Sir68k/md-classic-display/source/md_display/icons.h

#ifndef ICONS_7X7_H
#define ICONS_7X7_H

const static uint8_t icons_7x7[][7] = {
    {0x7f, 0x45, 0x49, 0x51, 0x49, 0x45, 0x7f}, //0 email
    {0x3e, 0x6f, 0x51, 0x01, 0x71, 0x7f, 0x3e}, //1 github
    {0x40, 0x60, 0x77, 0x77, 0x77, 0x60, 0x40}, //2 user
    {0x70, 0x7e, 0x71, 0x51, 0x71, 0x7e, 0x70}, //3 lock, password
    {0x08, 0x3e, 0x36, 0x63, 0x36, 0x3e, 0x08}, //4 cog, settings
    {0x3e, 0x63, 0x41, 0x4d, 0x49, 0x63, 0x3e}, //5 clock
    {0x0e, 0x11, 0x11, 0x11, 0x3e, 0x60, 0x40}, //6 search
    {0x7e, 0x3f, 0x15, 0x15, 0x1d, 0x1f, 0x0e}, //7 message
    {0x00, 0x22, 0x14, 0x7f, 0x49, 0x36, 0x00}, //8 bluetooth
    {0x1c, 0x3e, 0x3e, 0x3e, 0x3e, 0x3e, 0x3e}, //9 battery 100%
    {0x1c, 0x3e, 0x22, 0x3e, 0x3e, 0x3e, 0x3e}, //10 battery 75%
    {0x1c, 0x3e, 0x22, 0x22, 0x3e, 0x3e, 0x3e}, //11 battery 50%
    {0x1c, 0x3e, 0x22, 0x22, 0x22, 0x3e, 0x3e}, //12 battery 25%
    {0x1c, 0x3e, 0x22, 0x22, 0x22, 0x22, 0x3e}, //13 battery 0%
    {0x77, 0x41, 0x41, 0x00, 0x41, 0x41, 0x77}, //14 full screen
    {0x22, 0x63, 0x00, 0x00, 0x00, 0x63, 0x22}, //15 small screen
    {0x02, 0x7a, 0x4b, 0x7b, 0x4b, 0x7a, 0x02}, //16 trash, remove, delete
    {0x3c, 0x42, 0x43, 0x52, 0x53, 0x42, 0x3c}, //17 calendar
    {0x3e, 0x41, 0x5d, 0x58, 0x54, 0x42, 0x31}, //18 minimize
    {0x3e, 0x41, 0x41, 0x48, 0x45, 0x43, 0x37}, //19 maximize
    {0x3c, 0x24, 0x77, 0x55, 0x77, 0x24, 0x3c}, //20 printer
    {0x1c, 0x1c, 0x1c, 0x22, 0x77, 0x77, 0x77}, //21 share
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
    {0x3e, 0x41, 0x65, 0x51, 0x65, 0x41, 0x3e}, //138 smile 2
    {0x3e, 0x41, 0x55, 0x51, 0x55, 0x41, 0x3e}, //139 smile 3
    {0x3e, 0x41, 0x45, 0x51, 0x45, 0x41, 0x3e}, //140 smile 4
    {0x3e, 0x41, 0x4d, 0x61, 0x4d, 0x41, 0x3e}, //141 smile 5
    {0x01, 0x03, 0x7f, 0x5d, 0x55, 0x55, 0x7f}, //142 sms
    {0x1e, 0x3f, 0x3f, 0x3f, 0x33, 0x33, 0x1e}, //143 toggle on
    {0x1e, 0x2d, 0x2d, 0x21, 0x21, 0x21, 0x1e}, //144 toggle off
    {0x00, 0x00, 0x7f, 0x3e, 0x1c, 0x08, 0x00}, //145 arrow type 1 right
    {0x00, 0x08, 0x1c, 0x3e, 0x7f, 0x00, 0x00}, //146 arrow type 1 left
    {0x04, 0x0c, 0x1c, 0x3c, 0x1c, 0x0c, 0x04}, //147 arrow type 1 down
    {0x10, 0x18, 0x1c, 0x1e, 0x1c, 0x18, 0x10}, //148 arrow type 1 up
    {0x08, 0x08, 0x08, 0x7f, 0x3e, 0x1c, 0x08}, //149 arrow type 2 right
    {0x08, 0x1c, 0x3e, 0x7f, 0x08, 0x08, 0x08}, //150 arrow type 2 left
    {0x08, 0x18, 0x38, 0x7f, 0x38, 0x18, 0x08}, //151 arrow type 2 down
    {0x08, 0x0c, 0x0e, 0x7f, 0x0e, 0x0c, 0x08}, //152 arrow type 2 up
    {0x02, 0x39, 0x44, 0x54, 0x44, 0x39, 0x02}, //153 alarm clock
    {0x1c, 0x22, 0x1c, 0x08, 0x18, 0x08, 0x38}, //154 key
};


#endif //ICONS_7X7_H
