Sir68k/md-classic-display/source/md_display/sony_font.h

#pragma once

// Font copied from MZ-N510 display

#define SONY_FONT_HEIGHT 7
#define SONY_FONT_WIDTH  6

const uint8_t _sonyFont[][7] = {
  { 0x3f, 0x3f, 0x3f, 0x3f, 0x3f, 0x3f, 0x3f },
  { 0x3f, 0x3f, 0x3f, 0x3f, 0x3f, 0x3f, 0x1 },
  { 0x3f, 0x3f, 0x3f, 0x3f, 0x3f, 0x1, 0x3f },
  { 0x3f, 0x3f, 0x3f, 0x3f, 0x1, 0x3f, 0x3f },
  { 0x3f, 0x3f, 0x3f, 0x1, 0x3f, 0x3f, 0x3f },
  { 0x3f, 0x3f, 0x1, 0x3f, 0x3f, 0x3f, 0x3f },
  { 0x3f, 0x1, 0x3f, 0x3f, 0x3f, 0x3f, 0x3f },
  { 0x1, 0x3f, 0x3f, 0x3f, 0x3f, 0x3f, 0x3f },
  { 0x0, 0x0, 0x0, 0x0, 0x0, 0x0, 0x0 },
  { 0x0, 0x0, 0x0, 0x0, 0x0, 0x0, 0x3e },
  { 0x0, 0x0, 0x0, 0x0, 0x0, 0x3e, 0x0 },
  { 0x0, 0x0, 0x0, 0x0, 0x3e, 0x0, 0x0 },
  { 0x0, 0x0, 0x0, 0x3e, 0x0, 0x0, 0x0 },
  { 0x0, 0x0, 0x3e, 0x0, 0x0, 0x0, 0x0 },
  { 0x0, 0x3e, 0x0, 0x0, 0x0, 0x0, 0x0 },
  { 0x3e, 0x0, 0x0, 0x0, 0x0, 0x0, 0x0 },
  { 0x0, 0x0, 0x0, 0x0, 0x0, 0x0, 0x0 },
  { 0x8, 0x8, 0x8, 0x8, 0x8, 0x0, 0x8 },
  { 0x12, 0x24, 0x0, 0x0, 0x0, 0x0, 0x0 },
  { 0x14, 0x3e, 0x14, 0x14, 0x14, 0x3e, 0x14 },
  { 0x8, 0x1e, 0x28, 0x1c, 0xa, 0x3c, 0x8 },
  { 0x30, 0x32, 0x4, 0x8, 0x10, 0x26, 0x6 },
  { 0x10, 0x28, 0x28, 0x12, 0x2a, 0x24, 0x1a },
  { 0x8, 0x10, 0x0, 0x0, 0x0, 0x0, 0x0 },
  { 0x4, 0x8, 0x10, 0x10, 0x10, 0x8, 0x4 },
  { 0x10, 0x8, 0x4, 0x4, 0x4, 0x8, 0x10 },
  { 0x0, 0x8, 0x2a, 0x1c, 0x2a, 0x8, 0x0 },
  { 0x0, 0x8, 0x8, 0x3e, 0x8, 0x8, 0x0 },
  { 0x0, 0x0, 0x0, 0x0, 0x0, 0x8, 0x10 },
  { 0x0, 0x0, 0x0, 0x3e, 0x0, 0x0, 0x0 },
  { 0x0, 0x0, 0x0, 0x0, 0x0, 0x0, 0x10 },
  { 0x0, 0x2, 0x4, 0x8, 0x10, 0x20, 0x0 },
  { 0x1c, 0x22, 0x26, 0x2a, 0x32, 0x22, 0x1c },
  { 0x2, 0xe, 0x2, 0x2, 0x2, 0x2, 0x2 },
  { 0x1c, 0x22, 0x2, 0xc, 0x10, 0x20, 0x3e },
  { 0x1c, 0x22, 0x2, 0xc, 0x2, 0x22, 0x1c },
  { 0x4, 0xc, 0x14, 0x24, 0x3e, 0x4, 0x4 },
  { 0x3e, 0x20, 0x3c, 0x2, 0x2, 0x22, 0x1c },
  { 0xc, 0x10, 0x20, 0x3c, 0x22, 0x22, 0x1c },
  { 0x3e, 0x2, 0x4, 0x4, 0x8, 0x8, 0x8 },
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
};
